amonbenson/expresso/expresso/src/midi/encoding/usb.rs

use super::super::{DecodeResult, MidiDecoder, MidiEncoder, MidiMessage, PacketSink};

pub struct UsbMidiEncoder;

impl MidiEncoder for UsbMidiEncoder {
    type Packet = [u8; 4];

    fn emit<S>(&mut self, message: &MidiMessage, sink: &mut S) -> Result<(), S::Error>
    where
        S: PacketSink<Packet = [u8; 4]>,
    {
        match message {
            MidiMessage::NoteOn {
                channel,
                note,
                velocity,
            } => sink.emit([0x09, 0x90 | (channel & 0x0F), *note, *velocity])?,
            MidiMessage::NoteOff {
                channel,
                note,
                velocity,
            } => sink.emit([0x08, 0x80 | (channel & 0x0F), *note, *velocity])?,
            MidiMessage::ControlChange {
                channel,
                control,
                value,
            } => sink.emit([0x0B, 0xB0 | (channel & 0x0F), *control, *value])?,
            MidiMessage::ProgramChange { channel, program } => {
                sink.emit([0x0C, 0xC0 | (channel & 0x0F), *program, 0x00])?
            }
            MidiMessage::PitchBend { channel, value } => {
                let u = (*value + 8192) as u16;
                sink.emit([
                    0x0E,
                    0xE0 | (channel & 0x0F),
                    (u & 0x7F) as u8,
                    ((u >> 7) & 0x7F) as u8,
                ])?;
            }
        }
        Ok(())
    }
}

impl UsbMidiEncoder {
    /// Encode a raw SysEx payload (must include leading 0xF0 and trailing 0xF7)
    /// into USB MIDI packets and emit them to `sink`.
    pub fn emit_sysex<S>(&mut self, payload: &[u8], sink: &mut S) -> Result<(), S::Error>
    where
        S: PacketSink<Packet = [u8; 4]>,
    {
        let mut i = 0;
        while i < payload.len() {
            let remaining = payload.len() - i;
            let packet = match remaining {
                1 => [0x05, payload[i], 0x00, 0x00],
                2 => [0x06, payload[i], payload[i + 1], 0x00],
                r if r >= 3 && i + 3 >= payload.len() => {
                    [0x07, payload[i], payload[i + 1], payload[i + 2]]
                }
                _ => [0x04, payload[i], payload[i + 1], payload[i + 2]],
            };
            sink.emit(packet)?;
            i += 3;
        }
        Ok(())
    }
}

// ---- USB MIDI Decoder ----

pub struct UsbMidiDecoder<const SYSEX_N: usize> {
    sysex_buf: [u8; SYSEX_N],
    sysex_len: usize,
    in_sysex: bool,
}

impl<const SYSEX_N: usize> UsbMidiDecoder<SYSEX_N> {
    pub fn new() -> Self {
        Self {
            sysex_buf: [0; SYSEX_N],
            sysex_len: 0,
            in_sysex: false,
        }
    }

    fn push_sysex(&mut self, byte: u8) {
        if self.sysex_len < SYSEX_N {
            self.sysex_buf[self.sysex_len] = byte;
            self.sysex_len += 1;
        }
    }
}

impl<const SYSEX_N: usize> MidiDecoder for UsbMidiDecoder<SYSEX_N> {
    type Packet = [u8; 4];

    fn feed(&mut self, packet: [u8; 4]) -> Option<DecodeResult<'_>> {
        let cin = packet[0] & 0x0F;
        let status = packet[1];
        let d1 = packet[2];
        let d2 = packet[3];
        let channel = status & 0x0F;

        match cin {
            0x04 => {
                self.in_sysex = true;
                self.push_sysex(packet[1]);
                self.push_sysex(packet[2]);
                self.push_sysex(packet[3]);
                None
            }
            0x05 | 0x06 | 0x07 => {
                let count = (cin - 0x04) as usize;
                for &b in &packet[1..=count] {
                    self.push_sysex(b);
                }
                self.in_sysex = false;
                let len = self.sysex_len;
                self.sysex_len = 0;
                Some(DecodeResult::Sysex(&self.sysex_buf[..len]))
            }
            0x08 => Some(DecodeResult::Message(MidiMessage::NoteOff {
                channel,
                note: d1,
                velocity: d2,
            })),
            0x09 => Some(DecodeResult::Message(if d2 == 0 {
                MidiMessage::NoteOff {
                    channel,
                    note: d1,
                    velocity: 0,
                }
            } else {
                MidiMessage::NoteOn {
                    channel,
                    note: d1,
                    velocity: d2,
                }
            })),
            0x0B => Some(DecodeResult::Message(MidiMessage::ControlChange {
                channel,
                control: d1,
                value: d2,
            })),
            0x0C => Some(DecodeResult::Message(MidiMessage::ProgramChange {
                channel,
                program: d1,
            })),
            0x0E => {
                let raw = (d1 as u16) | ((d2 as u16) << 7);
                Some(DecodeResult::Message(MidiMessage::PitchBend {
                    channel,
                    value: raw as i16 - 8192,
                }))
            }
            _ => None,
        }
    }

    fn reset(&mut self) {
        self.sysex_len = 0;
        self.in_sysex = false;
    }
}

// ---- Tests ----

#[cfg(test)]
mod tests {
    use super::*;
    use crate::midi::encoding::test_utils::CollectSink;

    mod usb_encoder {
        use super::*;

        fn encode(message: &MidiMessage) -> CollectSink<[u8; 4], 16> {
            let mut encoder = UsbMidiEncoder;
            let mut sink = CollectSink::new();
            encoder.emit(message, &mut sink).unwrap();
            sink
        }

        fn encode_sysex(payload: &[u8]) -> CollectSink<[u8; 4], 16> {
            let mut encoder = UsbMidiEncoder;
            let mut sink = CollectSink::new();
            encoder.emit_sysex(payload, &mut sink).unwrap();
            sink
        }

        #[test]
        fn note_on() {
            let sink = encode(&MidiMessage::NoteOn {
                channel: 0,
                note: 60,
                velocity: 100,
            });
            assert_eq!(sink.len(), 1);
            assert_eq!(sink.get(0), [0x09, 0x90, 60, 100]);
        }

        #[test]
        fn note_on_channel() {
            let sink = encode(&MidiMessage::NoteOn {
                channel: 5,
                note: 60,
                velocity: 100,
            });
            assert_eq!(sink.get(0), [0x09, 0x95, 60, 100]);
        }

        #[test]
        fn note_on_channel_clamped() {
            let sink = encode(&MidiMessage::NoteOn {
                channel: 0xFF,
                note: 60,
                velocity: 100,
            });
            assert_eq!(sink.get(0)[1] & 0x0F, 0x0F);
        }

        #[test]
        fn note_off() {
            let sink = encode(&MidiMessage::NoteOff {
                channel: 0,
                note: 60,
                velocity: 64,
            });
            assert_eq!(sink.len(), 1);
            assert_eq!(sink.get(0), [0x08, 0x80, 60, 64]);
        }

        #[test]
        fn control_change() {
            let sink = encode(&MidiMessage::ControlChange {
                channel: 2,
                control: 7,
                value: 127,
            });
            assert_eq!(sink.len(), 1);
            assert_eq!(sink.get(0), [0x0B, 0xB2, 7, 127]);
        }

        #[test]
        fn program_change() {
            let sink = encode(&MidiMessage::ProgramChange {
                channel: 0,
                program: 42,
            });
            assert_eq!(sink.len(), 1);
            assert_eq!(sink.get(0), [0x0C, 0xC0, 42, 0x00]);
        }

        #[test]
        fn pitch_bend_center() {
            let sink = encode(&MidiMessage::PitchBend {
                channel: 0,
                value: 0,
            });
            assert_eq!(sink.len(), 1);
            assert_eq!(sink.get(0), [0x0E, 0xE0, 0x00, 0x40]);
        }

        #[test]
        fn pitch_bend_max() {
            let sink = encode(&MidiMessage::PitchBend {
                channel: 0,
                value: 8191,
            });
            assert_eq!(sink.len(), 1);
            assert_eq!(sink.get(0), [0x0E, 0xE0, 0x7F, 0x7F]);
        }

        #[test]
        fn pitch_bend_min() {
            let sink = encode(&MidiMessage::PitchBend {
                channel: 0,
                value: -8192,
            });
            assert_eq!(sink.len(), 1);
            assert_eq!(sink.get(0), [0x0E, 0xE0, 0x00, 0x00]);
        }

        #[test]
        fn sysex_single_packet() {
            // F0 + 1 data byte + F7 = 3 bytes, fits in one CIN 0x07 end packet
            let data = [0xF0, 0x41, 0xF7];
            let sink = encode_sysex(&data);
            assert_eq!(sink.len(), 1);
            assert_eq!(sink.get(0)[0] & 0x0F, 0x07);
        }

        #[test]
        fn sysex_multiple_packets() {
            // F0 + 6 data bytes + F7 = 8 bytes total
            let data = [0xF0, 0x01, 0x02, 0x03, 0x04, 0x05, 0x06, 0xF7];
            let sink = encode_sysex(&data);
            assert_eq!(sink.len(), 3);
            assert_eq!(sink.get(0)[0] & 0x0F, 0x04);
            assert_eq!(sink.get(1)[0] & 0x0F, 0x04);
            assert_eq!(sink.get(2)[0] & 0x0F, 0x06);
        }

        #[test]
        fn note_on_note_and_velocity_values() {
            let sink = encode(&MidiMessage::NoteOn { channel: 0, note: 72, velocity: 42 });
            assert_eq!(sink.get(0)[2], 72);
            assert_eq!(sink.get(0)[3], 42);
        }

        #[test]
        fn note_off_note_and_velocity_values() {
            let sink = encode(&MidiMessage::NoteOff { channel: 0, note: 55, velocity: 80 });
            assert_eq!(sink.get(0)[2], 55);
            assert_eq!(sink.get(0)[3], 80);
        }

        #[test]
        fn sysex_end_1_byte() {
            // F0 + 2 data bytes + F7 = 4 bytes; first CIN 0x04, last F7 alone (CIN 0x05)
            let data = [0xF0, 0x41, 0x10, 0xF7];
            let sink = encode_sysex(&data);
            let last = sink.get(sink.len() - 1);
            assert_eq!(last[0] & 0x0F, 0x05);
        }
    }

    mod usb_decoder {
        use super::*;

        fn decode(packet: [u8; 4]) -> Option<MidiMessage> {
            let mut decoder = UsbMidiDecoder::<0>::new();
            match decoder.feed(packet) {
                Some(DecodeResult::Message(msg)) => Some(msg),
                _ => None,
            }
        }

        #[test]
        fn note_on() {
            let msg = decode([0x09, 0x92, 60, 100]).unwrap();
            assert!(matches!(
                msg,
                MidiMessage::NoteOn {
                    channel: 2,
                    note: 60,
                    velocity: 100
                }
            ));
        }

        // Destructures result fields directly instead of using matches!, covering
        // the note/velocity bindings in the 0x08 and 0x09 decoder arms.
        #[test]
        fn note_on_channel_note_velocity() {
            let msg = decode([0x09, 0x97, 72, 42]).unwrap();
            match msg {
                MidiMessage::NoteOn { channel, note, velocity } => {
                    assert_eq!(channel, 7);
                    assert_eq!(note, 72);
                    assert_eq!(velocity, 42);
                }
                _ => panic!("expected NoteOn"),
            }
        }

        #[test]
        fn note_off_channel_note_velocity() {
            let msg = decode([0x08, 0x8B, 55, 80]).unwrap();
            match msg {
                MidiMessage::NoteOff { channel, note, velocity } => {
                    assert_eq!(channel, 11);
                    assert_eq!(note, 55);
                    assert_eq!(velocity, 80);
                }
                _ => panic!("expected NoteOff"),
            }
        }

        #[test]
        fn note_on_velocity_zero_becomes_note_off() {
            let msg = decode([0x09, 0x90, 60, 0]).unwrap();
            assert!(matches!(
                msg,
                MidiMessage::NoteOff {
                    channel: 0,
                    note: 60,
                    velocity: 0
                }
            ));
        }

        #[test]
        fn note_off() {
            let msg = decode([0x08, 0x83, 48, 64]).unwrap();
            assert!(matches!(
                msg,
                MidiMessage::NoteOff {
                    channel: 3,
                    note: 48,
                    velocity: 64
                }
            ));
        }

        #[test]
        fn control_change() {
            let msg = decode([0x0B, 0xB1, 7, 127]).unwrap();
            assert!(matches!(
                msg,
                MidiMessage::ControlChange {
                    channel: 1,
                    control: 7,
                    value: 127
                }
            ));
        }

        #[test]
        fn program_change() {
            let msg = decode([0x0C, 0xC0, 42, 0x00]).unwrap();
            assert!(matches!(
                msg,
                MidiMessage::ProgramChange {
                    channel: 0,
                    program: 42
                }
            ));
        }

        #[test]
        fn pitch_bend_center() {
            let msg = decode([0x0E, 0xE0, 0x00, 0x40]).unwrap();
            assert!(matches!(
                msg,
                MidiMessage::PitchBend {
                    channel: 0,
                    value: 0
                }
            ));
        }

        #[test]
        fn pitch_bend_min() {
            let msg = decode([0x0E, 0xE0, 0x00, 0x00]).unwrap();
            assert!(matches!(
                msg,
                MidiMessage::PitchBend {
                    channel: 0,
                    value: -8192
                }
            ));
        }

        #[test]
        fn unknown_cin_returns_none() {
            assert!(decode([0x00, 0x00, 0x00, 0x00]).is_none());
            assert!(decode([0x01, 0x00, 0x00, 0x00]).is_none());
            assert!(decode([0x0F, 0x00, 0x00, 0x00]).is_none());
        }

        #[test]
        fn sysex_single_packet() {
            let mut decoder = UsbMidiDecoder::<64>::new();
            let result = decoder.feed([0x07, 0xF0, 0x41, 0xF7]);
            match result {
                Some(DecodeResult::Sysex(data)) => assert_eq!(data, &[0xF0, 0x41, 0xF7]),
                _ => panic!("expected sysex"),
            }
        }

        #[test]
        fn sysex_multi_packet() {
            let mut decoder = UsbMidiDecoder::<64>::new();
            assert!(decoder.feed([0x04, 0xF0, 0x01, 0x02]).is_none());
            assert!(decoder.feed([0x04, 0x03, 0x04, 0x05]).is_none());
            let result = decoder.feed([0x06, 0x06, 0xF7, 0x00]);
            match result {
                Some(DecodeResult::Sysex(data)) => {
                    assert_eq!(data, &[0xF0, 0x01, 0x02, 0x03, 0x04, 0x05, 0x06, 0xF7]);
                }
                _ => panic!("expected sysex"),
            }
        }

        #[test]
        fn reset_clears_sysex_state() {
            let mut decoder = UsbMidiDecoder::<64>::new();
            assert!(decoder.feed([0x04, 0xF0, 0x01, 0x02]).is_none());
            decoder.reset();
            let result = decoder.feed([0x09, 0x90, 60, 100]);
            assert!(matches!(
                result,
                Some(DecodeResult::Message(MidiMessage::NoteOn { .. }))
            ));
        }
    }

    mod usb_roundtrip {
        use super::*;

        fn roundtrip(message: &MidiMessage) -> Option<MidiMessage> {
            let mut encoder = UsbMidiEncoder;
            let mut sink = CollectSink::<[u8; 4], 16>::new();
            encoder.emit(message, &mut sink).unwrap();

            let mut decoder = UsbMidiDecoder::<256>::new();
            let mut result = None;
            for i in 0..sink.len() {
                if let Some(packet) = sink.buf[i] {
                    if let Some(DecodeResult::Message(msg)) = decoder.feed(packet) {
                        result = Some(msg);
                    }
                }
            }
            result
        }

        #[test]
        fn note_on_roundtrip() {
            let msg = MidiMessage::NoteOn {
                channel: 3,
                note: 64,
                velocity: 80,
            };
            assert!(matches!(
                roundtrip(&msg).unwrap(),
                MidiMessage::NoteOn {
                    channel: 3,
                    note: 64,
                    velocity: 80
                }
            ));
        }

        #[test]
        fn note_off_roundtrip() {
            let msg = MidiMessage::NoteOff {
                channel: 1,
                note: 48,
                velocity: 0,
            };
            assert!(matches!(
                roundtrip(&msg).unwrap(),
                MidiMessage::NoteOff {
                    channel: 1,
                    note: 48,
                    velocity: 0
                }
            ));
        }

        #[test]
        fn control_change_roundtrip() {
            let msg = MidiMessage::ControlChange {
                channel: 0,
                control: 74,
                value: 64,
            };
            assert!(matches!(
                roundtrip(&msg).unwrap(),
                MidiMessage::ControlChange {
                    channel: 0,
                    control: 74,
                    value: 64
                }
            ));
        }

        #[test]
        fn program_change_roundtrip() {
            let msg = MidiMessage::ProgramChange {
                channel: 2,
                program: 10,
            };
            assert!(matches!(
                roundtrip(&msg).unwrap(),
                MidiMessage::ProgramChange {
                    channel: 2,
                    program: 10
                }
            ));
        }

        #[test]
        fn pitch_bend_roundtrip_center() {
            let msg = MidiMessage::PitchBend {
                channel: 0,
                value: 0,
            };
            assert!(matches!(
                roundtrip(&msg).unwrap(),
                MidiMessage::PitchBend {
                    channel: 0,
                    value: 0
                }
            ));
        }

        #[test]
        fn pitch_bend_roundtrip_max() {
            let msg = MidiMessage::PitchBend {
                channel: 0,
                value: 8191,
            };
            assert!(matches!(
                roundtrip(&msg).unwrap(),
                MidiMessage::PitchBend {
                    channel: 0,
                    value: 8191
                }
            ));
        }

        #[test]
        fn pitch_bend_roundtrip_min() {
            let msg = MidiMessage::PitchBend {
                channel: 0,
                value: -8192,
            };
            assert!(matches!(
                roundtrip(&msg).unwrap(),
                MidiMessage::PitchBend {
                    channel: 0,
                    value: -8192
                }
            ));
        }

        #[test]
        fn sysex_roundtrip() {
            let data = [0xF0, 0x41, 0x10, 0x42, 0x12, 0x01, 0x02, 0x03, 0xF7];

            let mut encoder = UsbMidiEncoder;
            let mut sink = CollectSink::<[u8; 4], 16>::new();
            encoder.emit_sysex(&data, &mut sink).unwrap();

            let mut decoder = UsbMidiDecoder::<64>::new();
            for i in 0..sink.len() {
                if let Some(packet) = sink.buf[i] {
                    if let Some(DecodeResult::Sysex(decoded)) = decoder.feed(packet) {
                        assert_eq!(decoded, &data);
                        return;
                    }
                }
            }
            panic!("no sysex message produced");
        }
    }
}
